pvphan/tinycam/cad/hqcam.FCStd

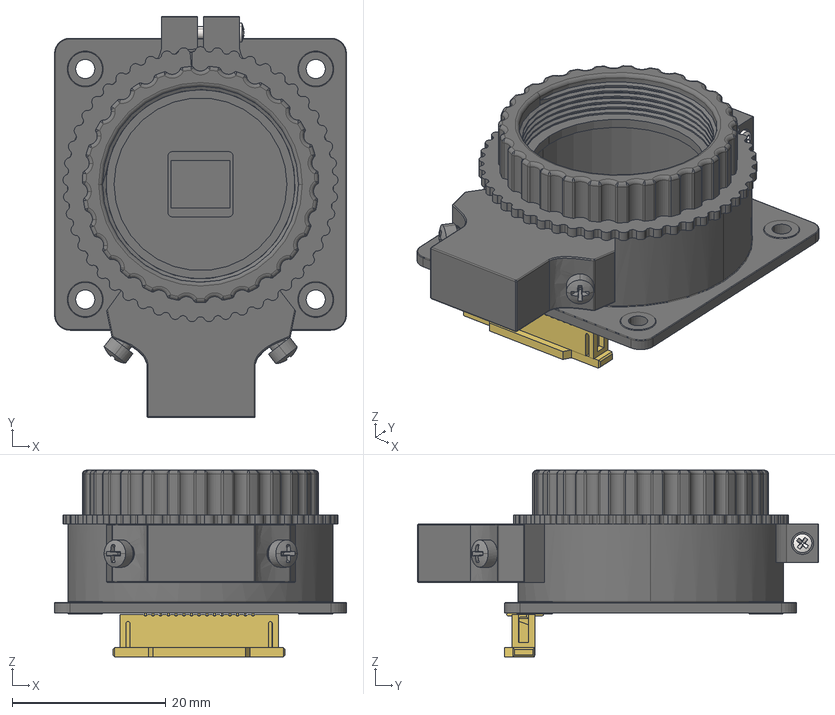
[picture p21: CAD file, 2020-08-09]
cad/hqcam.FCStd
38.0 x 52.2 x 24.3 mm
Raspberry Pi HQ Camera.
fillister head screw_ai_CR-FIMS 0.086-64x0.188x0.188-N
fillister head screw_ai_CR-FIMS 0.086-64x0.188x0.188-N001
fillister head screw_ai_CR-FIMS 0.06-80x0.3125x0.3125-N
Camera Connector from RPi4ModelB
