pvphan/tinycam/cad/PowerBoost1000C.FCStd

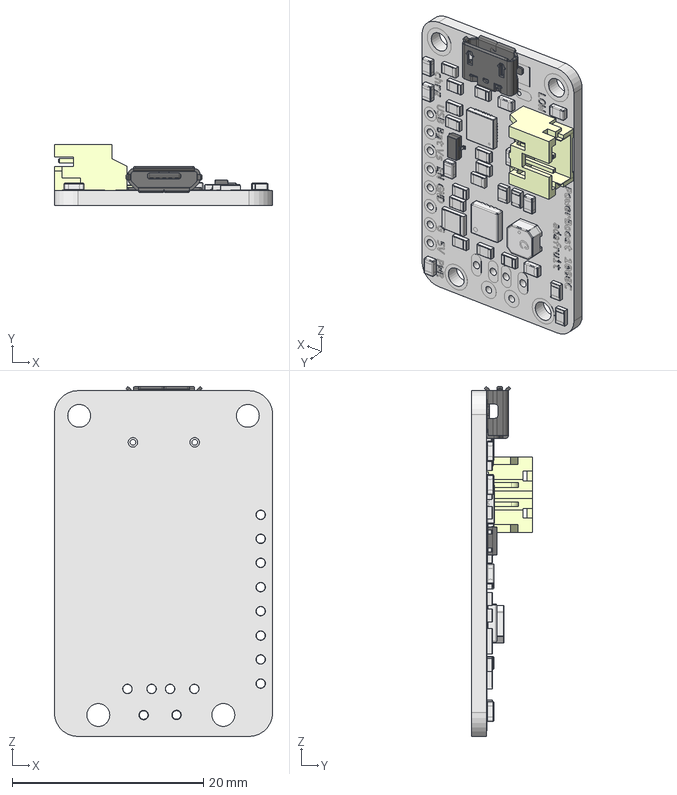
[picture p22: CAD file, 2020-08-09]
cad/PowerBoost1000C.FCStd
22.9 x 6.39 x 36.6 mm
PlacaSuperboost1000C
MicroUSB
pin
pin001
pin002
Molex2pinSMD
CAPC-0805-T0.75-BN
CAPC-0805-T0.75-BN001
CAPC-0805-T0.75-BN002
CAPC-0805-T0.75-BN003
CAPC-0805-T0.75-BN004
RESC-0805
RESC-0806
RESC-0807
RESC-0808
RESC-0809
RESC-0810
RESC-0811
RESC-0812
RESC-0813
RESC-0814
RESC-0815
RESC-0816
RESC-0817
RESC-0818
RESC-0819
RESC-0820
RESC-0821
RESC-0822
RESC-1210
LPS4018
MO-229W3030D-1_4000
MO-220WGGE
LED_SMD
LED_SMD001
LED_SMD002
LED_SMD003
