pvphan/tinycam/cad/telephotolens.FCStd

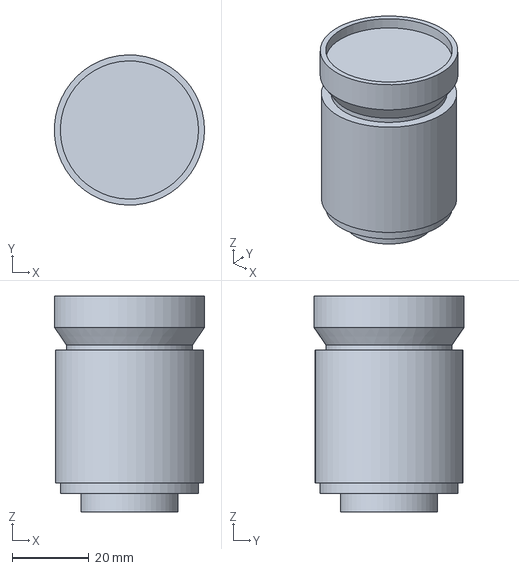
[picture p23: CAD file, 2020-08-09]
cad/telephotolens.FCStd
39.0 x 39.1 x 56.2 mm
