pvphan/tinycam/cad/picamadapter.fcstd

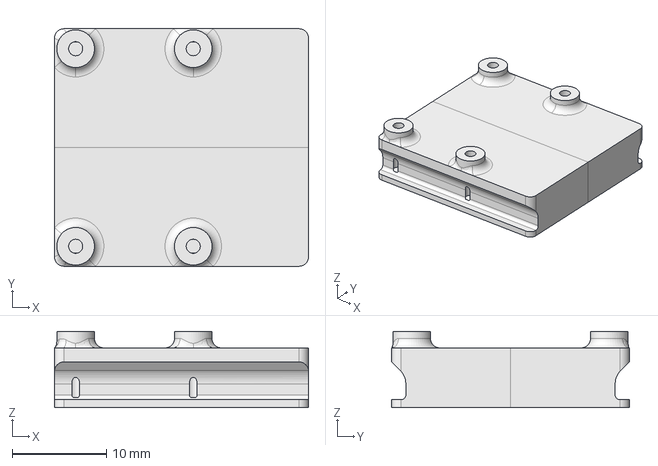
[picture p24: CAD file, 2020-08-09]
cad/picamadapter.fcstd
27.0 x 25.2 x 8.10 mm
