pvphan/tinycam/cad/lensmountbracket.FCStd

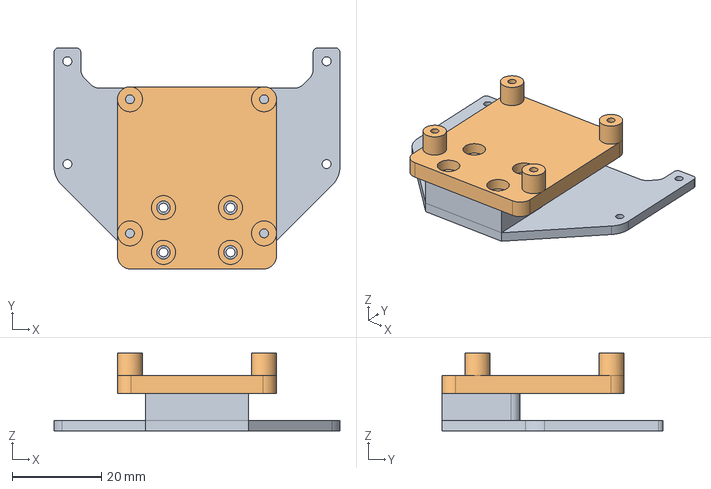
[picture p25: CAD file, 2020-08-09]
cad/lensmountbracket.FCStd
64.0 x 49.5 x 17.4 mm
body-piside
body-camside
