pvphan/tinycam/cad/rpizerow.FCStd

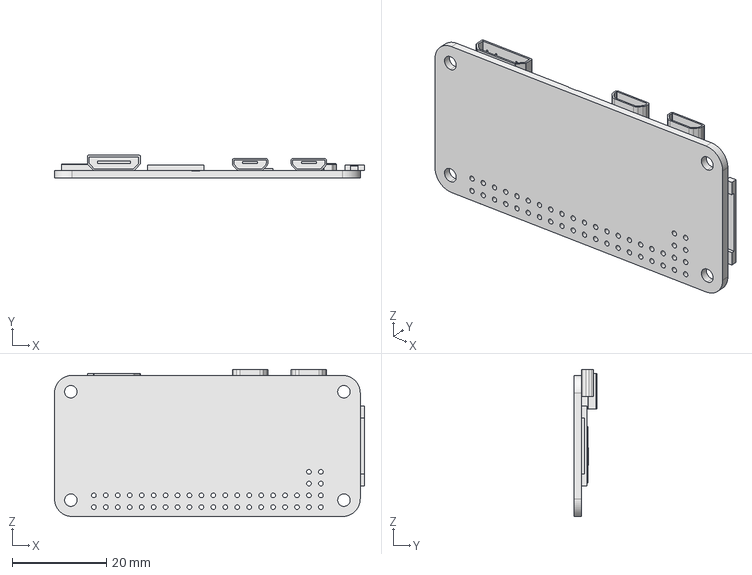
[picture p26: CAD file, 2020-08-09]
cad/rpizerow.FCStd
65.9 x 4.80 x 31.2 mm
